FilipNorlin/Split_Rail_Power_supply/ECAD/Kicad_lib/3d-models/TO-263-5.STEP

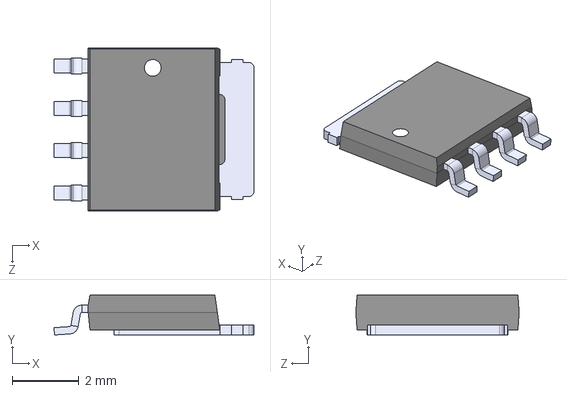
[picture p21: CAD file, 2026-09-20]
ECAD/Kicad_lib/3d-models/TO-263-5.STEP
6.00 x 1.20 x 4.90 mm
