FilipNorlin/Split_Rail_Power_supply/ECAD/Kicad_lib/3d-models/L_IHLP5050FD_5_0x5_0mm_Shielded.step

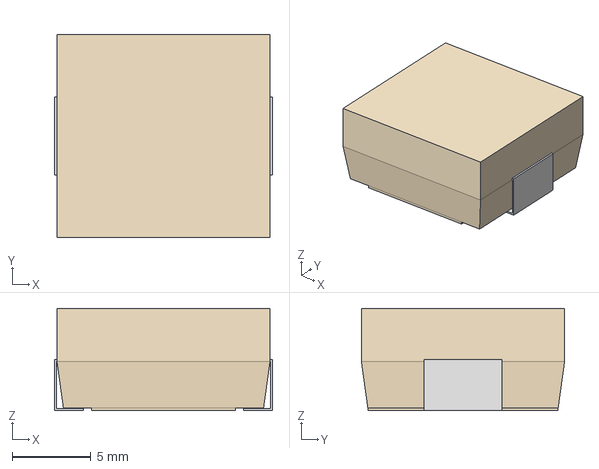
[picture p22: CAD file, 2026-09-20]
ECAD/Kicad_lib/3d-models/L_IHLP5050FD_5_0x5_0mm_Shielded.step
13.8 x 12.9 x 6.50 mm
