FilipNorlin/Split_Rail_Power_supply/ECAD/Kicad_lib/3d-models/Heat_Sink_TO-220_25mm.step

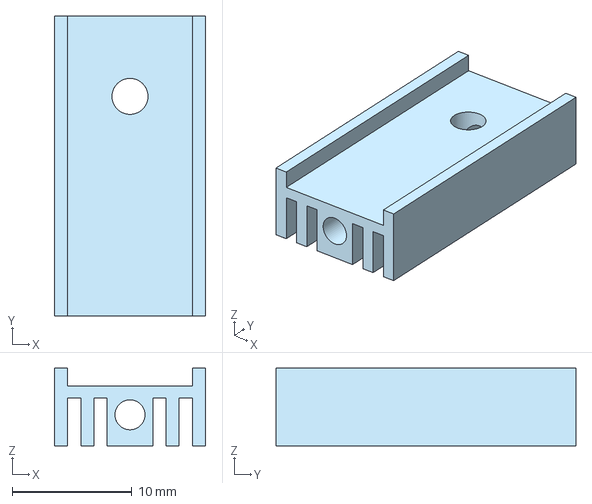
[picture p23: CAD file, 2026-09-20]
ECAD/Kicad_lib/3d-models/Heat_Sink_TO-220_25mm.step
12.6 x 25.0 x 6.50 mm
