FilipNorlin/Split_Rail_Power_supply/ECAD/Kicad_lib/3d-models/10_segment_bar_graph.step

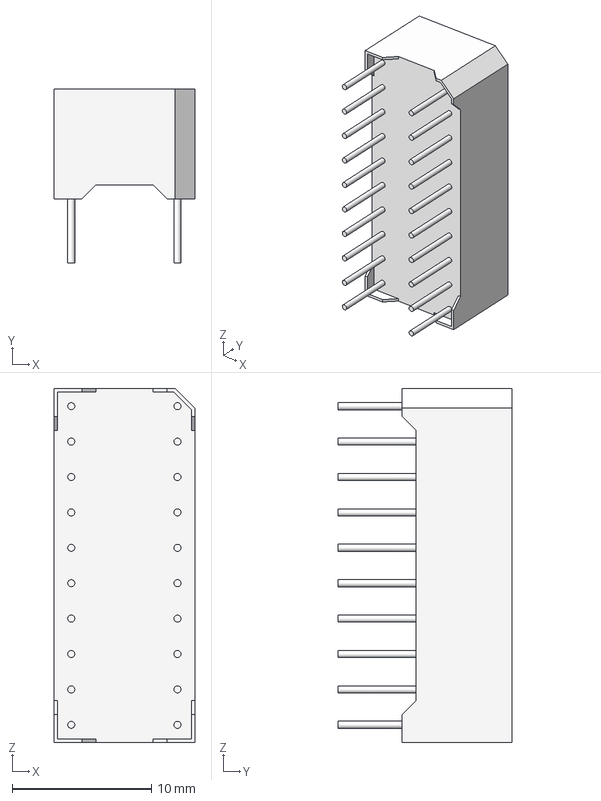
[picture p24: CAD file, 2026-09-20]
ECAD/Kicad_lib/3d-models/10_segment_bar_graph.step
10.1 x 12.5 x 25.4 mm
