FilipNorlin/Split_Rail_Power_supply/ECAD/Kicad_lib/3d-models/Resistor_Axial_Power_WW20W_27mm.stp

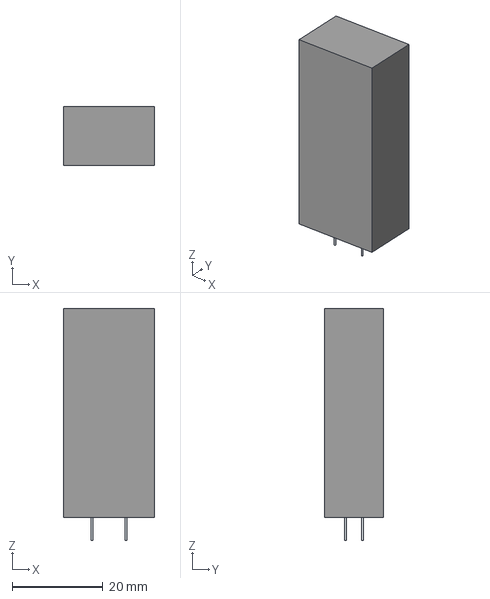
[picture p25: CAD file, 2026-09-20]
ECAD/Kicad_lib/3d-models/Resistor_Axial_Power_WW20W_27mm.stp
20.0 x 13.0 x 51.1 mm
Leads
