FilipNorlin/Split_Rail_Power_supply/ECAD/Kicad_lib/3d-models/RCJ-013.STEP

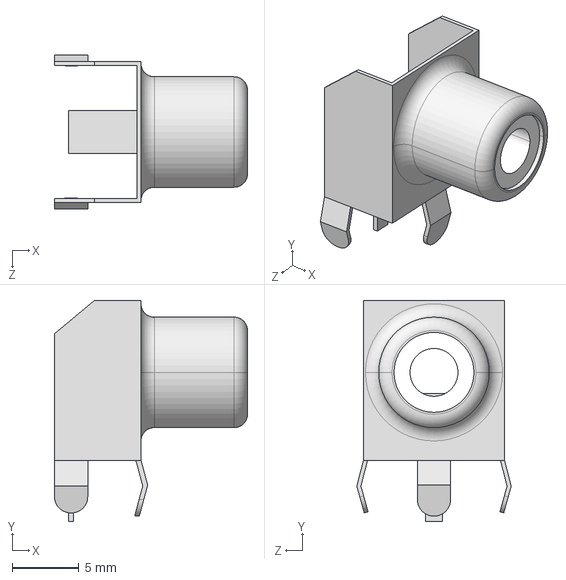
[picture p26: CAD file, 2026-09-20]
ECAD/Kicad_lib/3d-models/RCJ-013.STEP
14.5 x 16.6 x 11.6 mm
