FilipNorlin/Split_Rail_Power_supply/Simulation/Lt spice/test.asc

C1: cap; 1m
C2: cap; 1m
C3: cap; 1m
D1: diode; 1N4007
D2: diode; 1N4007
D3: diode; 1N5818
D4: diode; 1N5818
D5: diode; 1N5818
L1: ind; 1m
L2: ind; 470µ
L4: ind; 470µ
LP: ind; 100µ
LS1: ind; 100µ
LS2: ind; 100µ
M1: nmos; IRF530
M2: nmos; IRF530
R1: res; 50
R2: res; 50
V1: voltage; 50
V4: voltage; PULSE(0 10 0 0 0 0.3m 1m)
V5: voltage; PULSE(0 10 0 0 0 0.3m 1m)
Named nets: 0
K LP LS1 LS2 1
.tran 0 100m 90m
