FilipNorlin/Split_Rail_Power_supply/Simulation/Lt spice/2_swtich_forward_converter.asc

C1: cap; 1m
C2: cap; 470µ
D1: diode
D2: diode
D3: diode
D4: diode
L1: ind; 1m
L4: ind; 100µ
LP: ind; 100µ
LS: ind; 100µ
R1: res; 100
S1: sw
S2: sw
V1: voltage; 50
V2: voltage; PULSE(0 1 0 10n 10n {T*D} {T})
Named nets: 0, Vcon
K LP LS 1
.tran 0 1050m 1049.9m
.model sw sw(Ron = 1m, Roff = 10meg, Vt = 0.5, Vh = -0.5)
.model diode D(Ron = 1m, Roff = 10meg, Vfwd = 1m, epsilon = 1m)
.param D{1/3}
.param T 10u
