FilipNorlin/Split_Rail_Power_supply/Simulation/Lt spice/2_swtich_forward_converter_split_rail.asc

C1: cap; 1m
C2: cap; 1m
C3: cap; 1m
C4: cap; 1n
D1: diode
D2: diode
D3: diode
D4: diode
D5: diode
D6: diode
D7: diode
D8: diode
L1: ind; 1m
L2: ind; 470µ
L4: ind; 470µ
LP: ind; 100µ
LS1: ind; 100µ
LS2: ind; 100µ
R1: res; 100
R2: res; 100
R3: res; 1Meg
S1: sw
S2: sw
V1: voltage; 50
V2: voltage; PULSE(0 1 0 10n 10n {T*D} {T})
Named nets: 0, Vcon
K LP LS1 LS2 1
.tran 0 50m 49.9m
.param D{1/3}
.param T 10u
.model sw sw(Ron = 1m, Roff = 10meg, Vt = 0.5, Vh = -0.5)
.model diode D(Ron = 1m, Roff = 10meg, Vfwd = 1m, epsilon = 1m)
