FilipNorlin/Split_Rail_Power_supply/Simulation/Lt spice/diode_ringing_sim.asc

C1: cap; 1µ
C2: cap; 50p
D1: diode; Dbad
D2: diode; MBR735
L1: ind; 100n
R1: res; 100
R2: res; 1k
V1: voltage; PULSE(0 20 0 0.5ns 0.5ns 200ns 400ns)
Named nets: 0
.tran 0 101u 100u 1n
.model Dbad D (Cjo=200p Rs=0.1 Tt=200n)
