FilipNorlin/Split_Rail_Power_supply/Simulation/Lt spice/Draft1.asc

C1: cap; 1m
D1: diode
D2: diode
D3: diode
D4: diode
L1: ind; 1m
L2: ind; 400µ
LP: ind; 1m
LS1: ind; 1m
M1: nmos; IRF530
M2: nmos; IRF530
R1: res; 50
V1: voltage; 50
V2: voltage; PULSE(0 10 0 0 0 0.3m 1m)
V3: voltage; PULSE(0 5 0 0 0 0.3m 1m)
Named nets: 0, VSW1, VSW2
.tran 0 5.1 5 100u
K LP LS1 1
