FilipNorlin/Split_Rail_Power_supply/Simulation/Lt spice/Draft2.asc

C1: cap; 100µ
C2: cap; 100µ
D1: diode
D2: diode
D3: diode
L1: ind; 100µ
L2: ind; 100µ
L3: ind; 400µ
L4: ind; 100µ
R1: res; 10
S1: sw
V1: voltage; 10
V2: voltage; 0
V3: voltage
Named nets: 0, Vcon
