FilipNorlin/Split_Rail_Power_supply/ECAD/Kicad_lib/Design_Blocks/filip.kicad_blocks/USB_C_DATA.kicad_block/USB_C_DATA.kicad_sch

## KiCad design ECAD/Kicad_lib/Design_Blocks/filip.kicad_blocks/USB_C_DATA.kicad_block/USB_C_DATA.kicad_sch (2026-09-20)

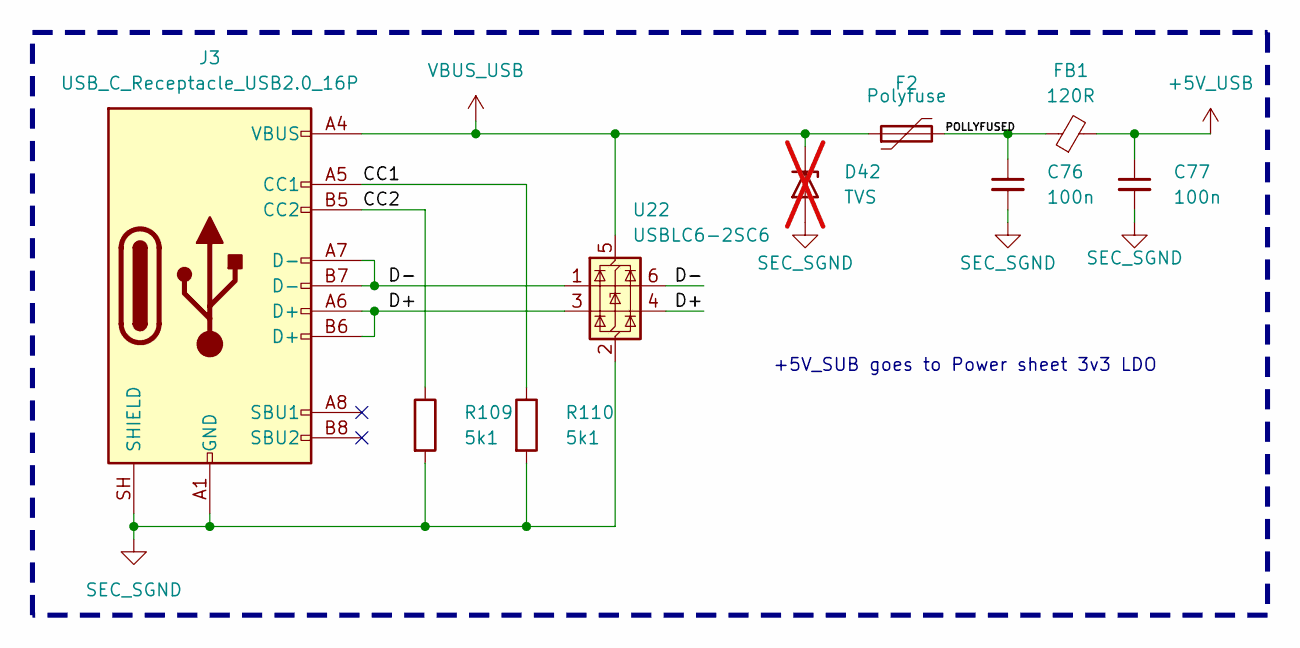
[picture p35: schematic USB_C_DATA.kicad_sch]

Parts:
C76, C77: 100n; C_0805_2012Metric
D42: TVS; D_SOD-523; Mouser No: 637-ESD5B5V0WT; not fitted
F2: Polyfuse; RV_Disc_D15.5mm_W5mm_P7.5mm; Mouser No: 576-60R050XU
FB1: 120R; L_0805_2012Metric
J3: USB_C_Receptacle_USB2.0_16P; USB_C_Receptacle_GCT_USB4105-xx-A_16P_TopMnt_Horizontal
R109, R110: 5k1; R_0805_2012Metric
U22: USBLC6-2SC6; SOT-23-6

Connections:
+5V_USB: C77.1, FB1.2
CC1: J3.A5 (CC1), R110.1
CC2: J3.B5 (CC2), R109.1
D+: J3.A6 (D+), J3.B6 (D+), U22.3 (I/O2), U22.4 (I/O2)
D-: J3.A7 (D-), J3.B7 (D-), U22.1 (I/O1), U22.6 (I/O1)
POLLYFUSED: C76.1, F2.2, FB1.1
SEC_SGND: C76.2, C77.2, D42.2 (A), J3.A1 (GND), J3.A12 (GND), J3.B1 (GND), J3.B12 (GND), J3.SH (SHIELD), R109.2, R110.2, U22.2 (GND)
VBUS_USB: D42.1 (K), F2.1, J3.A4 (VBUS), J3.A9 (VBUS), J3.B4 (VBUS), J3.B9 (VBUS), U22.5 (VBUS)

Notes on the sheet:
+5V_SUB goes to Power sheet 3v3 LDO
